MakerSpaceLeiden/sawblade-node/KiCad_files/sawblade-lock-node.kicad_sch

## KiCad design KiCad_files/sawblade-lock-node.kicad_sch (2023-10-23)

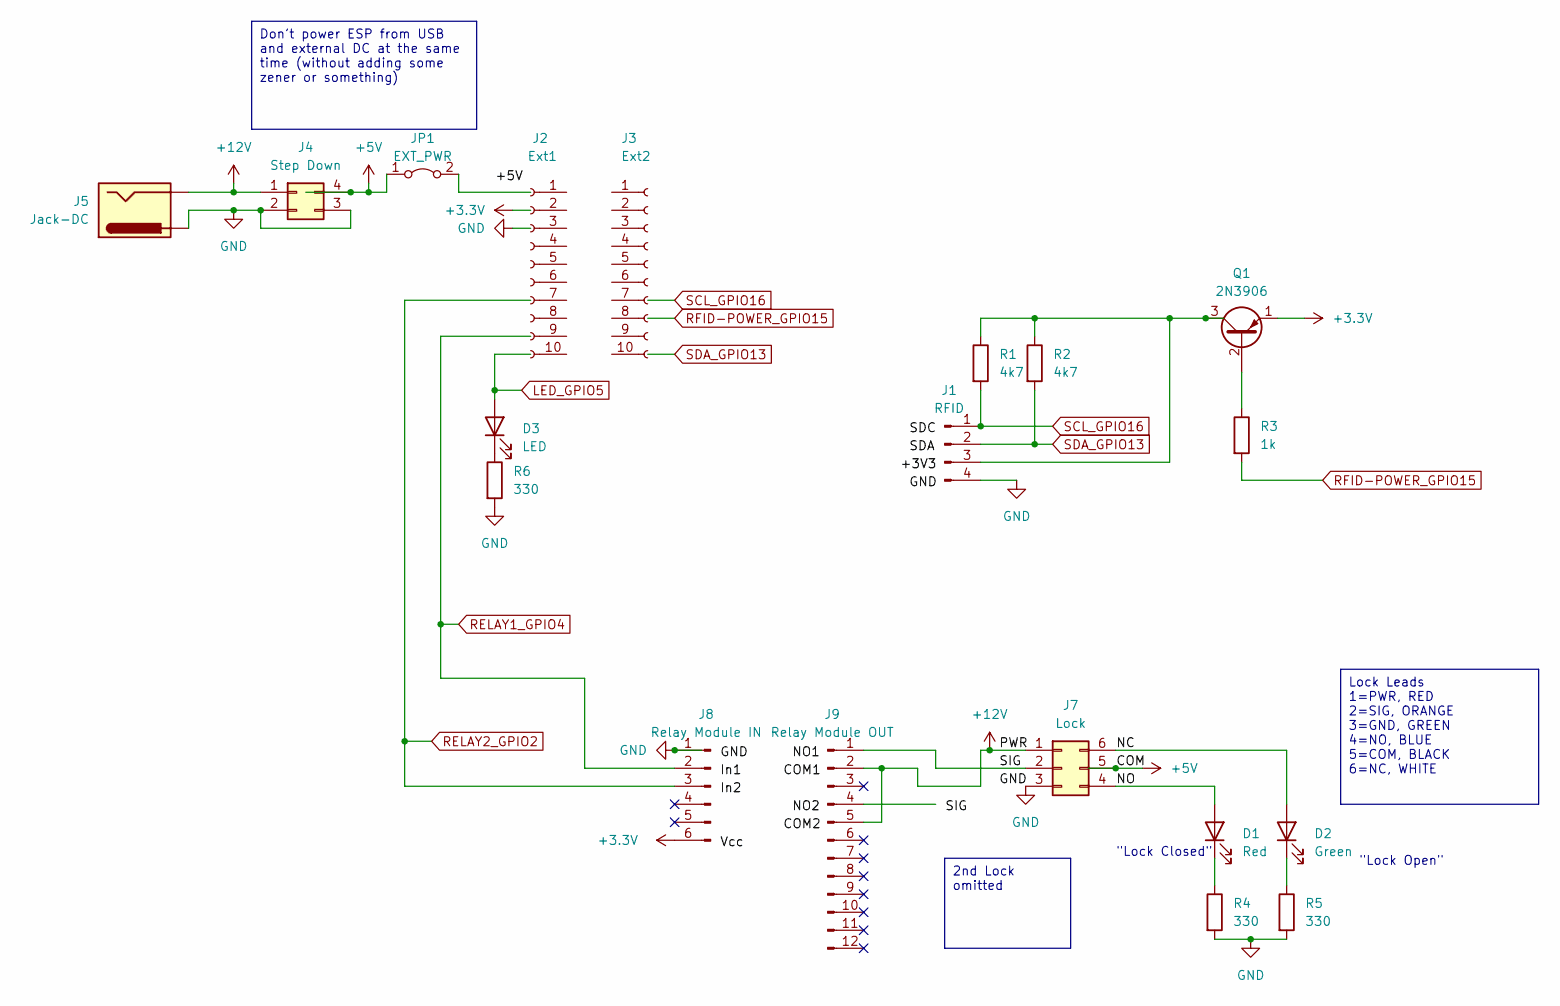
[picture p10: schematic sawblade-lock-node.kicad_sch]

Parts:
D1: Red
D2: Green
D3: LED
J1: RFID
J2: Ext1
J3: Ext2
J4: Step Down
J5: Jack-DC
J7: Lock
J8: Relay Module IN
J9: Relay Module OUT
JP1: EXT_PWR
Q1: 2N3906; TO-92_Inline
R1, R2: 4k7
R3: 1k
R4, R5, R6: 330

Connections:
+3.3V: J8.6, Q1.1 (E)
+5V: J4.4, J7.5, JP1.1 (A)
+12V: J4.1, J5.2, J7.1, J9.2, J9.5
GND: J1.4, J4.2, J4.3, J5.1, J7.3, J8.1, R4.2, R5.2, R6.2
LED_GPIO5: D3.2 (A)
NC: D2.2 (A), J7.6
NO: D1.2 (A), J7.4
unnamed: D1.1 (K), R4.1
unnamed: D2.1 (K), R5.1
unnamed: D3.1 (K), R6.1
unnamed: J1.3, Q1.3 (C), R1.1, R2.1
unnamed: Q1.2 (B), R3.1
RELAY1_GPIO4: J8.2
RELAY2_GPIO2: J8.3
RFID-POWER_GPIO15: R3.2
SCL_GPIO16: J1.1, R1.2
SDA_GPIO13: J1.2, R2.2
SIG: J7.2, J9.1

Notes on the sheet:
Lock Leads 1=PWR, RED 2=SIG, ORANGE 3=GND, GREEN 4=NO, BLUE 5=COM, BLACK 6=NC, WHITE
Don't power ESP from USB and external DC at the same time (without adding some zener or something)
2nd Lock omitted
"Lock Closed"
"Lock Open"
